JordiGuindo/pilot-in/distance_sensor.py

import RPi.GPIO as GPIO
import time
 
def distance(GPIO_TRIGGER, GPIO_ECHO):
    # Function to get distance via the distance sensor
    # Set Trigger to HIGH
    GPIO.output(GPIO_TRIGGER, True)
 
    # Set Trigger after 0.01ms to LOW
    time.sleep(0.00001)
    GPIO.output(GPIO_TRIGGER, False)
 
    StartTime = time.time()
    StopTime = time.time()
 
    # Save StartTime
    while GPIO.input(GPIO_ECHO) == 0:
        StartTime = time.time()
 
    # Save time of arrival
    while GPIO.input(GPIO_ECHO) == 1:
        StopTime = time.time()
 
    # Time difference between start and arrival
    TimeElapsed = StopTime - StartTime
    # Multiply with the sonic speed (34300 cm/s)
    # and divide by 2, because there and back
    distance = (TimeElapsed * 34300) / 2
 
    return distance
